Milk-Cool/cardtaiko/src/input.cpp

#include "input.h"
#include <Arduino.h>
#include <TouchyTouch.h>

#define MULT 1.035
#define ADD 50

TouchyTouch touch[4];
void init_input() {
    for(int i = 0; i < 4; i++) {
        // pins 1-4
        touch[i].begin(i + 1);
        touch[i].threshold *= MULT;
        touch[i].threshold += ADD;
    }
}
void recalibrate_input() {
    for(int i = 0; i < 4; i++) {
        touch[i].recalibrate();
        touch[i].threshold *= MULT;
        touch[i].threshold += ADD;
    }
}
uint8_t get_input() {
    for(int i = 0; i < 4; i++) touch[i].update();

    uint8_t mask = 0;
    if(touch[0].touched()) mask |= 1 << INPUT_KAT_LEFT;
    if(touch[1].touched()) mask |= 1 << INPUT_DON_LEFT;
    if(touch[2].touched()) mask |= 1 << INPUT_DON_RIGHT;
    if(touch[3].touched()) mask |= 1 << INPUT_KAT_RIGHT;
    if(BOOTSEL) mask |= 1 << INPUT_BOOTSEL;
    return mask;
}
bool check_input(uint8_t mask, uint8_t bit) {
    return !!(mask & (1 << bit));
}
